BZPJoe/bzp-airbridge/assets/remote-builder-mobile.png

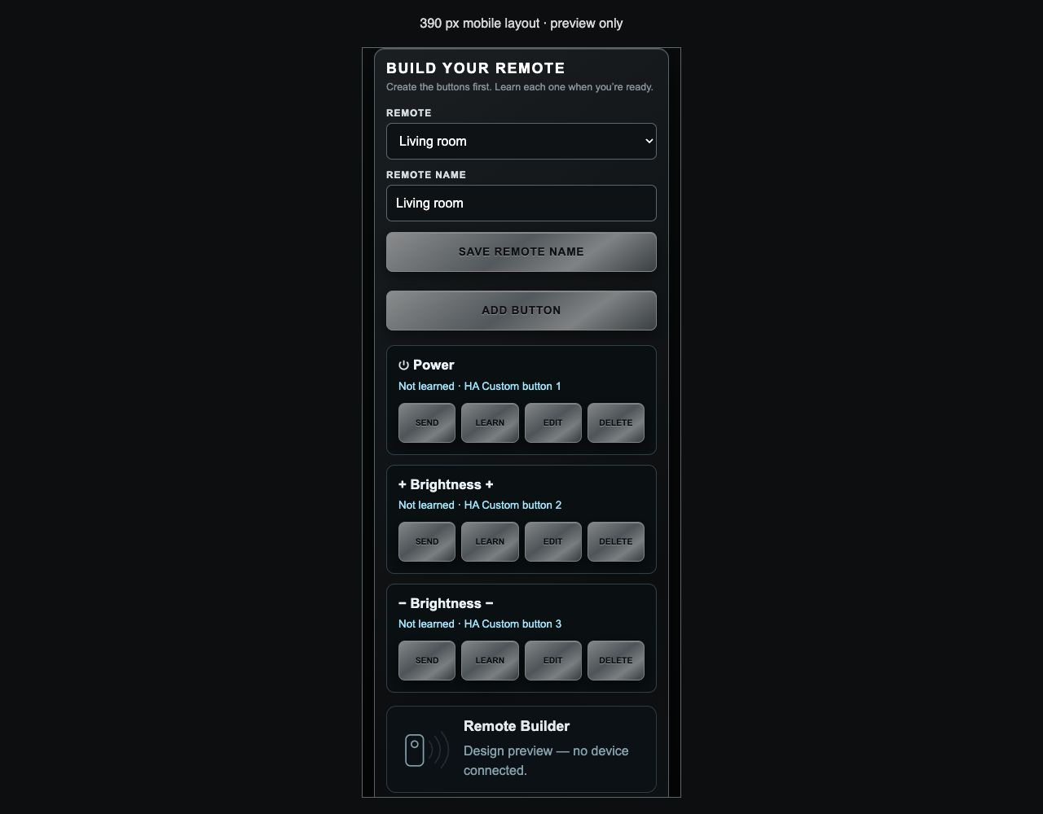
assets/remote-builder-mobile.png
