BZPJoe/bzp-airbridge/assets/remote-builder-preview.png

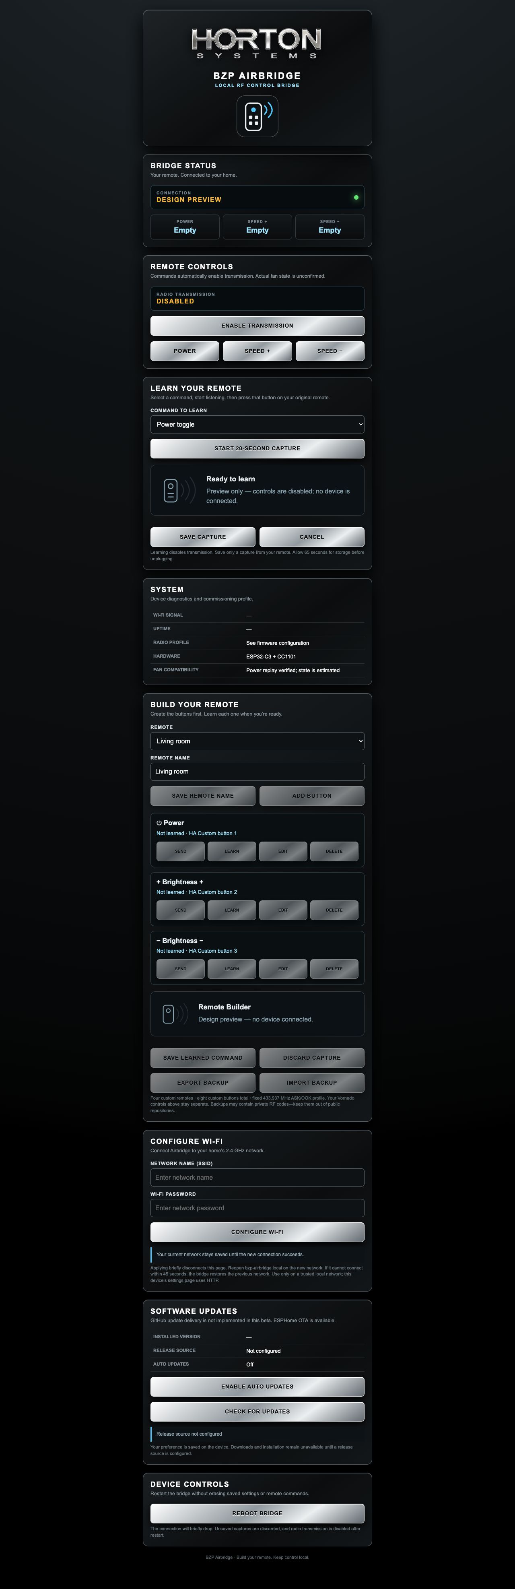
assets/remote-builder-preview.png
